BigCorvus/Physio/Pics/20170203_174452.jpg

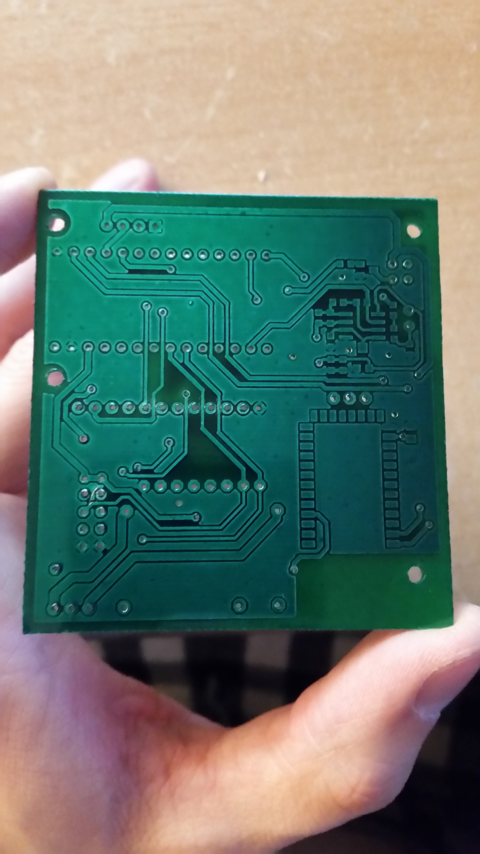
Pics/20170203_174452.jpg
