BigCorvus/Physio/Pics/20170203_174502.jpg

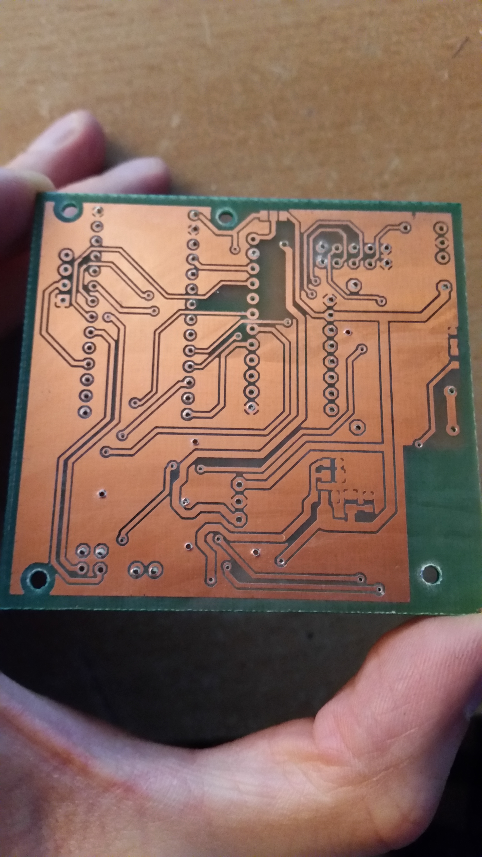
Pics/20170203_174502.jpg
