BigCorvus/Physio/Pics/Physio1.0inUse.jpg

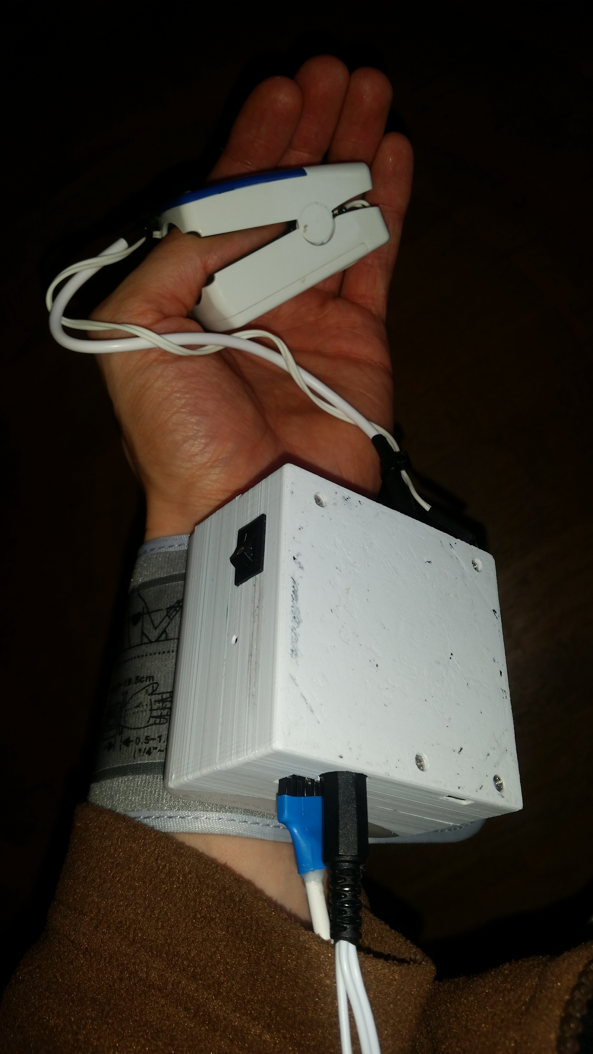
Pics/Physio1.0inUse.jpg
